blancoberg/arduino-motorcycle-gauge/bitmaps/_0002_Layer-1-copy.png

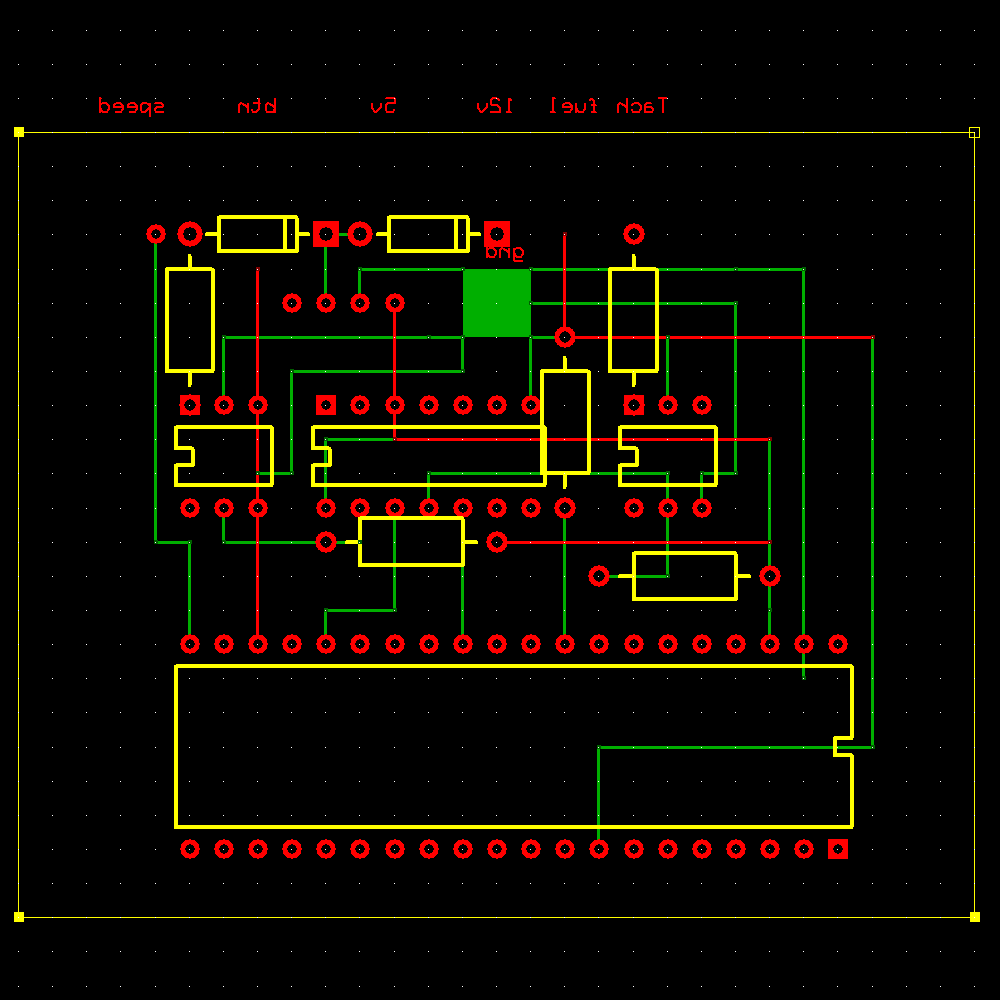
bitmaps/_0002_Layer-1-copy.png
