blancoberg/arduino-motorcycle-gauge/bitmaps/_0005_Layer-1.png

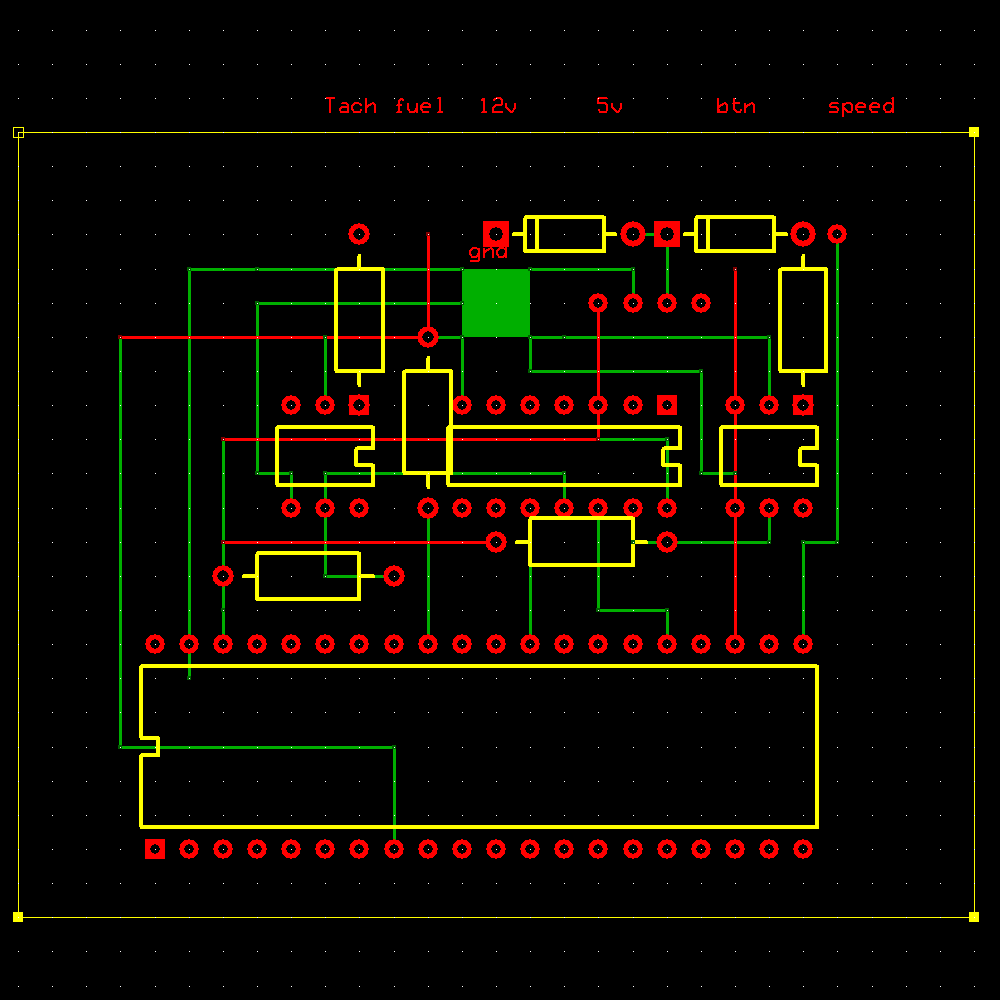
bitmaps/_0005_Layer-1.png
