blancoberg/arduino-motorcycle-gauge/motorcycle_gauge/_02_Scene_TripTotal.ino

class SceneTripTotal : public AbstractScene{

  public:
    SceneTripTotal() : AbstractScene() {};
    ~SceneTripTotal() {};
    void draw();

  private:
    double counter = 0.0;
    
};

void SceneTripTotal::draw(){

  drawRpm();
  drawFuel();
  drawSpeed();
  drawInfo("total",String(Odometer::distance/1000));
  
}
